wottle/lisa-mini-pi/software/lisa-pi-launcher/bitmap_font.py

"""A hand-rolled 5x7 dot-matrix bitmap font.

Deliberately not pygame.font/TTF - this project's whole visual premise is
authentic hard-edged 1-bit Lisa-era text, and a real font renderer brings
antialiasing and modern glyph shapes we don't want. Each glyph is 7 rows of
a 5-bit mask (bit 4 = leftmost column, bit 0 = rightmost column).
"""

import pygame

CHAR_WIDTH = 5
CHAR_HEIGHT = 7
_CHAR_SPACING = 1

# fmt: off
FONT: dict[str, tuple[int, int, int, int, int, int, int]] = {
    "A": (0b01110, 0b10001, 0b10001, 0b11111, 0b10001, 0b10001, 0b10001),
    "B": (0b11110, 0b10001, 0b10001, 0b11110, 0b10001, 0b10001, 0b11110),
    "C": (0b01111, 0b10000, 0b10000, 0b10000, 0b10000, 0b10000, 0b01111),
    "D": (0b11100, 0b10010, 0b10001, 0b10001, 0b10001, 0b10010, 0b11100),
    "E": (0b11111, 0b10000, 0b10000, 0b11110, 0b10000, 0b10000, 0b11111),
    "F": (0b11111, 0b10000, 0b10000, 0b11110, 0b10000, 0b10000, 0b10000),
    "G": (0b01111, 0b10000, 0b10000, 0b10011, 0b10001, 0b10001, 0b01111),
    "H": (0b10001, 0b10001, 0b10001, 0b11111, 0b10001, 0b10001, 0b10001),
    "I": (0b01110, 0b00100, 0b00100, 0b00100, 0b00100, 0b00100, 0b01110),
    "J": (0b00001, 0b00001, 0b00001, 0b00001, 0b10001, 0b10001, 0b01110),
    "K": (0b10001, 0b10010, 0b10100, 0b11000, 0b10100, 0b10010, 0b10001),
    "L": (0b10000, 0b10000, 0b10000, 0b10000, 0b10000, 0b10000, 0b11111),
    "M": (0b10001, 0b11011, 0b10101, 0b10101, 0b10001, 0b10001, 0b10001),
    "N": (0b10001, 0b11001, 0b10101, 0b10101, 0b10011, 0b10001, 0b10001),
    "O": (0b01110, 0b10001, 0b10001, 0b10001, 0b10001, 0b10001, 0b01110),
    "P": (0b11110, 0b10001, 0b10001, 0b11110, 0b10000, 0b10000, 0b10000),
    "Q": (0b01110, 0b10001, 0b10001, 0b10001, 0b10101, 0b10010, 0b01101),
    "R": (0b11110, 0b10001, 0b10001, 0b11110, 0b10100, 0b10010, 0b10001),
    "S": (0b01111, 0b10000, 0b10000, 0b01110, 0b00001, 0b00001, 0b11110),
    "T": (0b11111, 0b00100, 0b00100, 0b00100, 0b00100, 0b00100, 0b00100),
    "U": (0b10001, 0b10001, 0b10001, 0b10001, 0b10001, 0b10001, 0b01110),
    "V": (0b10001, 0b10001, 0b10001, 0b10001, 0b10001, 0b01010, 0b00100),
    "W": (0b10001, 0b10001, 0b10001, 0b10101, 0b10101, 0b10101, 0b01010),
    "X": (0b10001, 0b10001, 0b01010, 0b00100, 0b01010, 0b10001, 0b10001),
    "Y": (0b10001, 0b10001, 0b01010, 0b00100, 0b00100, 0b00100, 0b00100),
    "Z": (0b11111, 0b00001, 0b00010, 0b00100, 0b01000, 0b10000, 0b11111),
    "0": (0b01110, 0b10001, 0b10011, 0b10101, 0b11001, 0b10001, 0b01110),
    "1": (0b00100, 0b01100, 0b00100, 0b00100, 0b00100, 0b00100, 0b01110),
    "2": (0b01110, 0b10001, 0b00001, 0b00010, 0b00100, 0b01000, 0b11111),
    "3": (0b11111, 0b00010, 0b00100, 0b00010, 0b00001, 0b10001, 0b01110),
    "4": (0b00010, 0b00110, 0b01010, 0b10010, 0b11111, 0b00010, 0b00010),
    "5": (0b11111, 0b10000, 0b11110, 0b00001, 0b00001, 0b10001, 0b01110),
    "6": (0b00110, 0b01000, 0b10000, 0b11110, 0b10001, 0b10001, 0b01110),
    "7": (0b11111, 0b00001, 0b00010, 0b00100, 0b01000, 0b01000, 0b01000),
    "8": (0b01110, 0b10001, 0b10001, 0b01110, 0b10001, 0b10001, 0b01110),
    "9": (0b01110, 0b10001, 0b10001, 0b01111, 0b00001, 0b00010, 0b01100),
    " ": (0b00000, 0b00000, 0b00000, 0b00000, 0b00000, 0b00000, 0b00000),
    ".": (0b00000, 0b00000, 0b00000, 0b00000, 0b00000, 0b01100, 0b01100),
    ",": (0b00000, 0b00000, 0b00000, 0b00000, 0b00000, 0b00100, 0b01000),
    "/": (0b00001, 0b00010, 0b00010, 0b00100, 0b01000, 0b01000, 0b10000),
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
}
# fmt: on

_BLANK_GLYPH = (0, 0, 0, 0, 0, 0, 0)


def text_size(text: str, scale: int = 1) -> tuple[int, int]:
    if not text:
        return (0, CHAR_HEIGHT * scale)
    width = len(text) * CHAR_WIDTH + (len(text) - 1) * _CHAR_SPACING
    return (width * scale, CHAR_HEIGHT * scale)


def render_text(
    surface: pygame.Surface,
    text: str,
    x: int,
    y: int,
    scale: int = 1,
    color: tuple[int, int, int] = (0, 0, 0),
) -> pygame.Rect:
    cursor_x = x
    for ch in text.upper():
        glyph = FONT.get(ch, _BLANK_GLYPH)
        for row_index, row_bits in enumerate(glyph):
            for col_index in range(CHAR_WIDTH):
                bit = (row_bits >> (CHAR_WIDTH - 1 - col_index)) & 1
                if bit:
                    px = cursor_x + col_index * scale
                    py = y + row_index * scale
                    surface.fill(color, pygame.Rect(px, py, scale, scale))
        cursor_x += (CHAR_WIDTH + _CHAR_SPACING) * scale

    width, height = text_size(text, scale=scale)
    return pygame.Rect(x, y, width, height)
